wggm01/ISL-Maze-Solver-Robots/Robots/Fatima/GRAFICOS/SEGUNDO INTENTO.png

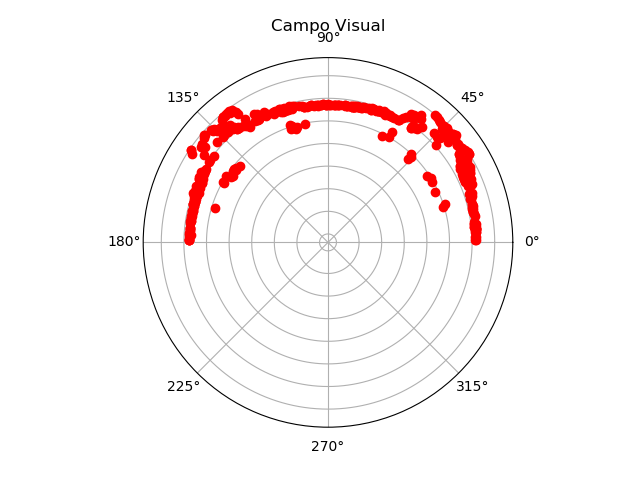
Robots/Fatima/GRAFICOS/SEGUNDO INTENTO.png
