wggm01/ISL-Maze-Solver-Robots/Robots/Fatima/IMUvi/data/texttest.png

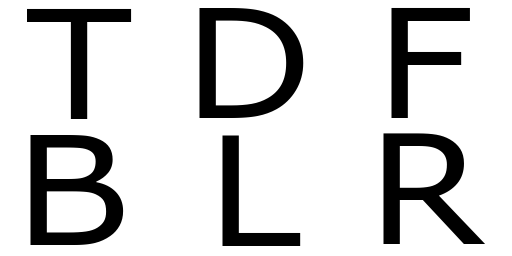
Robots/Fatima/IMUvi/data/texttest.png
