wggm01/ISL-Maze-Solver-Robots/Robots/Fatima/LSI.png

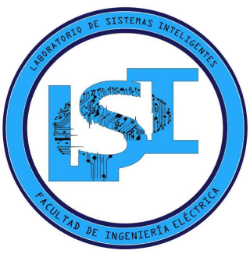
Robots/Fatima/LSI.png
