wggm01/ISL-Maze-Solver-Robots/Robots/Fatima/MEJORAS/3d83c7c686e7c798222806760055512f_1024x1024.png

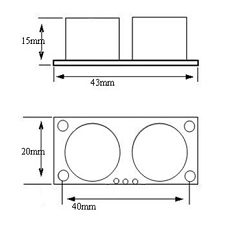
Robots/Fatima/MEJORAS/3d83c7c686e7c798222806760055512f_1024x1024.png
