wggm01/ISL-Maze-Solver-Robots/Robots/Fatima/MEJORAS/l298n.png

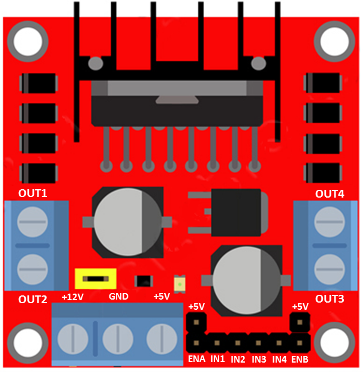
Robots/Fatima/MEJORAS/l298n.png
