wggm01/ISL-Maze-Solver-Robots/Robots/Fatima/MEJORAS/llanta definitiva.PNG

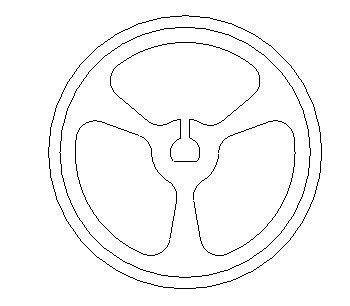
Robots/Fatima/MEJORAS/llanta definitiva.PNG
