wggm01/ISL-Maze-Solver-Robots/Robots/Fatima/MEJORAS/LLANTAS PARA SOPORTE EXTRAS.jpg

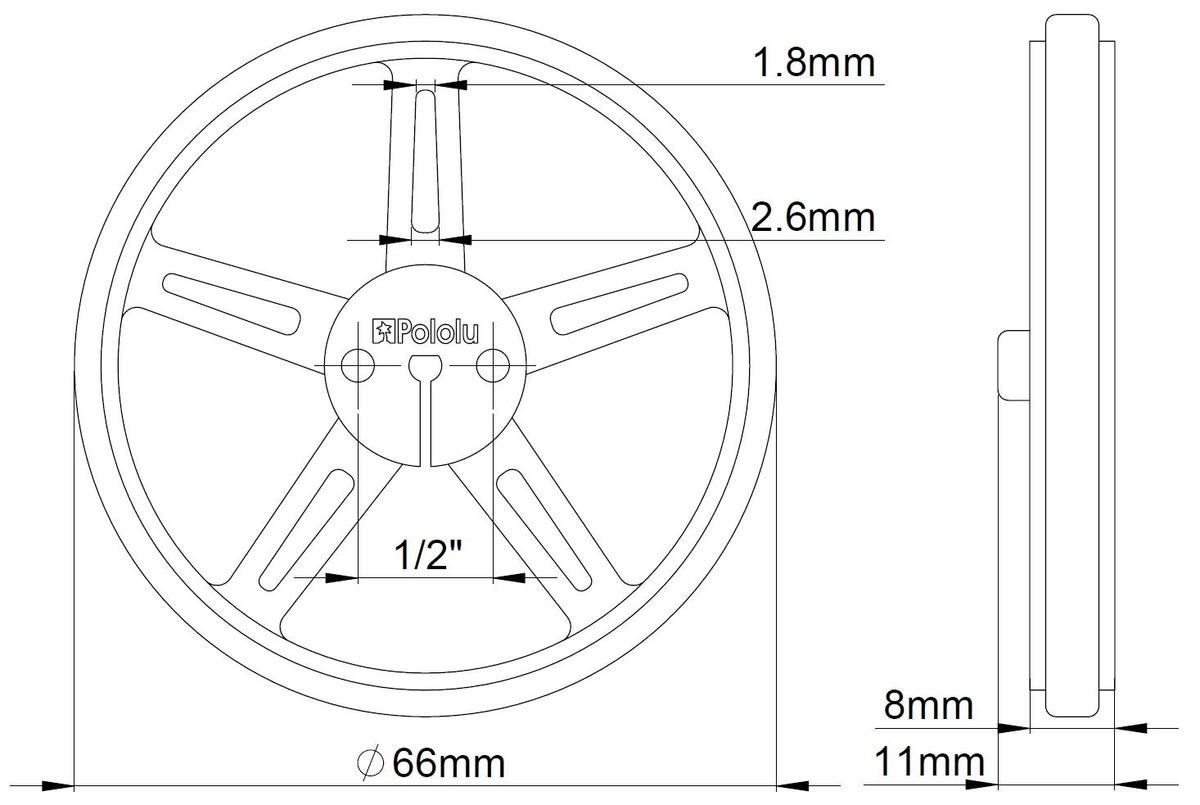
Robots/Fatima/MEJORAS/LLANTAS PARA SOPORTE EXTRAS.jpg
