wggm01/ISL-Maze-Solver-Robots/Robots/Fatima/MEJORAS/medidas servo.jpg

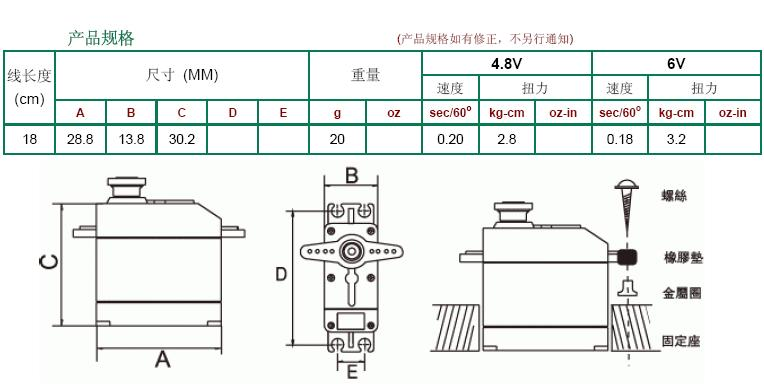
Robots/Fatima/MEJORAS/medidas servo.jpg
