wggm01/ISL-Maze-Solver-Robots/Robots/Fatima/MEJORAS/Nivel1.jpg

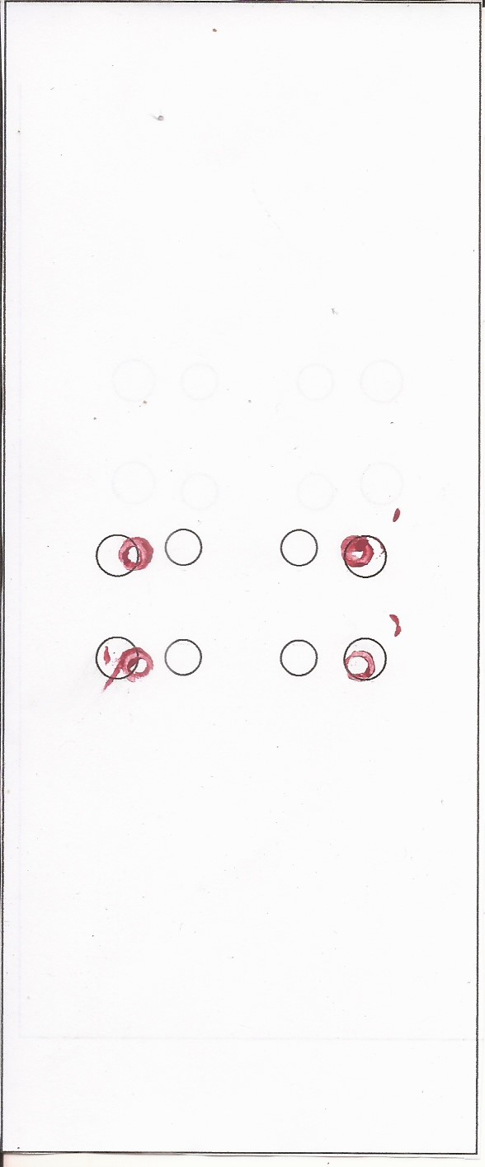
Robots/Fatima/MEJORAS/Nivel1.jpg
