wggm01/ISL-Maze-Solver-Robots/Robots/Fatima/MEJORAS/Nivel 3.jpg

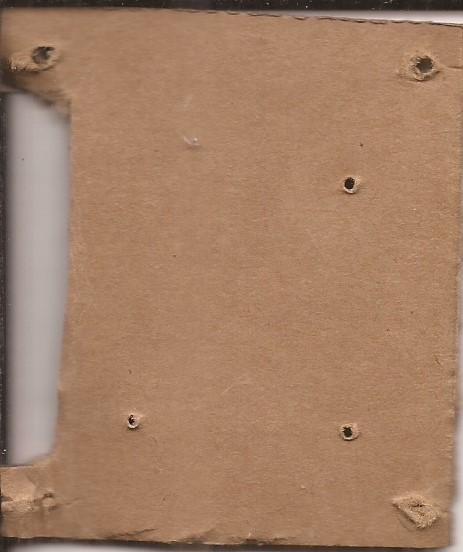
Robots/Fatima/MEJORAS/Nivel 3.jpg
