wggm01/ISL-Maze-Solver-Robots/Robots/Fatima/MEJORAS/NUEVA PCB MAY0 2019.png

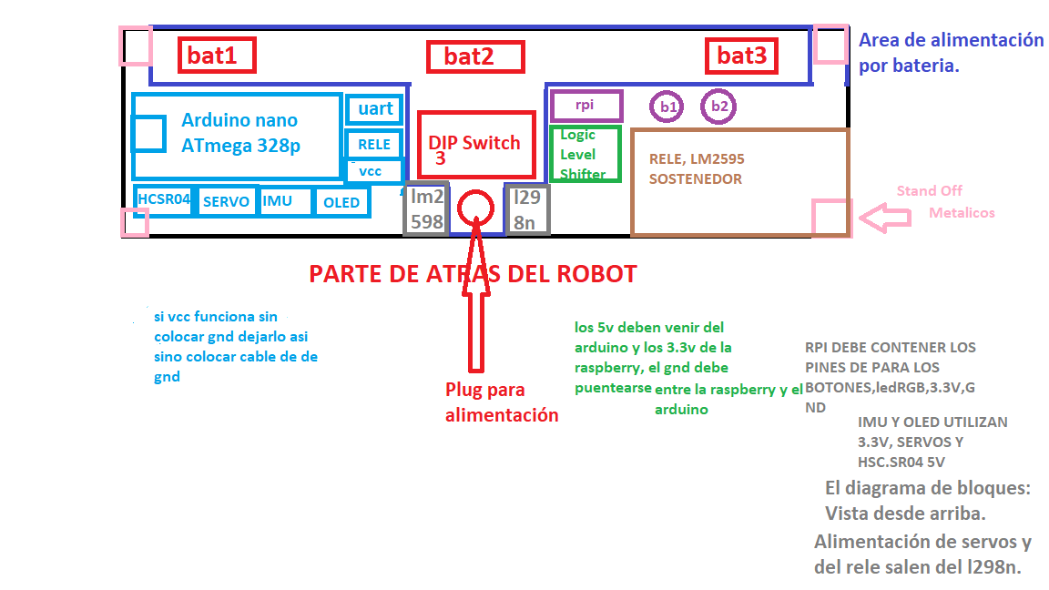
Robots/Fatima/MEJORAS/NUEVA PCB MAY0 2019.png
