wggm01/ISL-Maze-Solver-Robots/Robots/Fatima/MEJORAS/servo definitivo.PNG

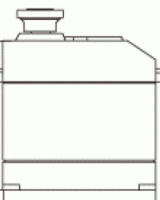
Robots/Fatima/MEJORAS/servo definitivo.PNG
