wggm01/ISL-Maze-Solver-Robots/Robots/Fatima/MEJORAS/union.jpg

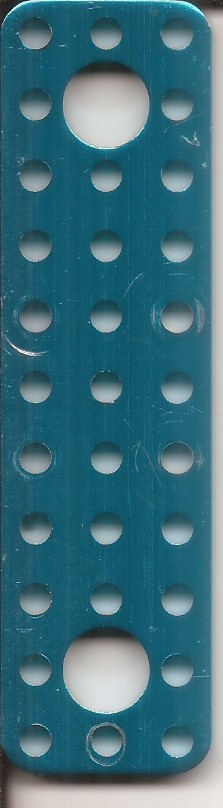
Robots/Fatima/MEJORAS/union.jpg
