wggm01/ISL-Maze-Solver-Robots/Robots/Gabriel/GCF-91B_1_/IMG_20181219_214946.jpg

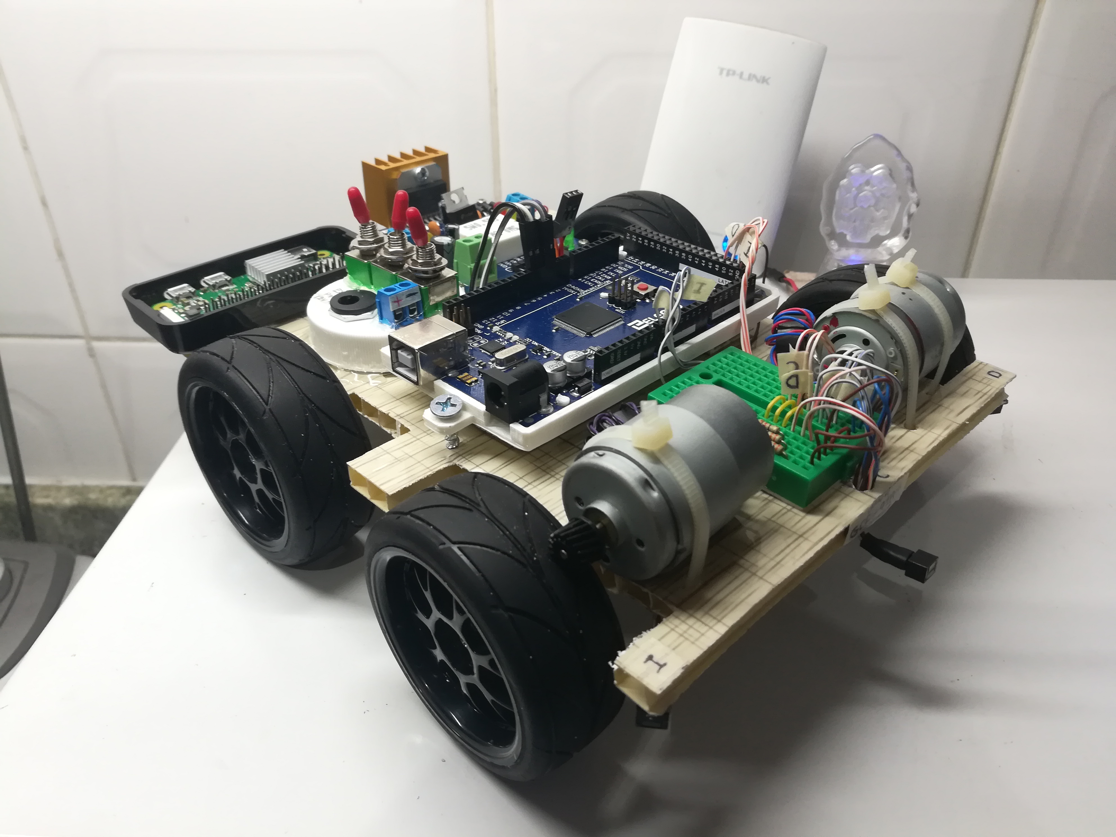
Robots/Gabriel/GCF-91B_1_/IMG_20181219_214946.jpg
