wggm01/ISL-Maze-Solver-Robots/Robots/Fatima/MEJORAS/sonar_cotas.dxf

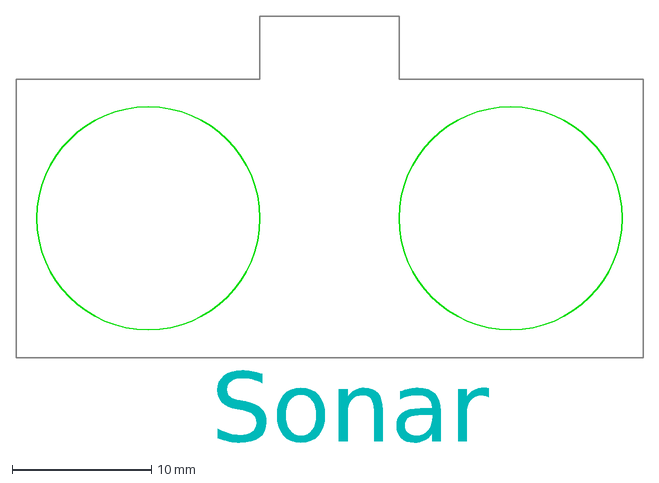
[picture p60: CAD file, 2019-03-16]
Robots/Fatima/MEJORAS/sonar_cotas.dxf
Sonar
