wggm01/ISL-Maze-Solver-Robots/Robots/Fatima/MEJORAS/CoverHCSR04.stl

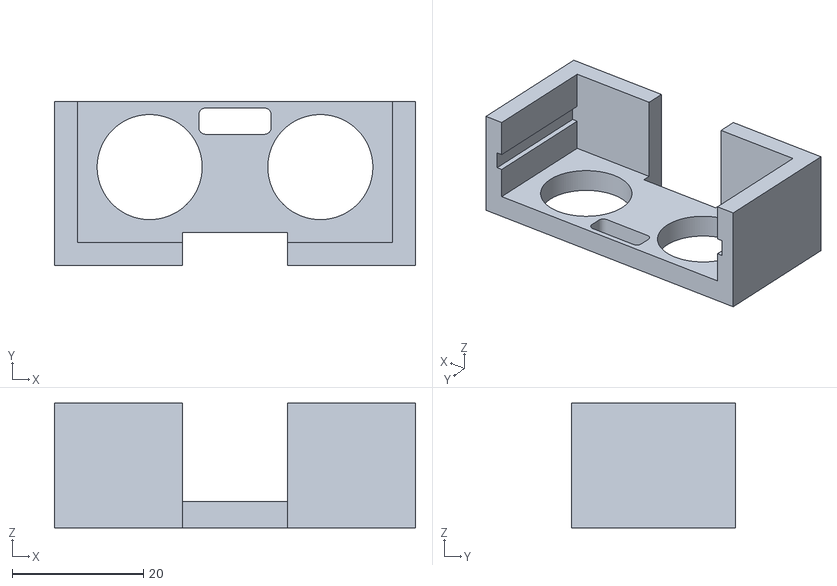
[picture p61: CAD file, 2019-03-16]
Robots/Fatima/MEJORAS/CoverHCSR04.stl
55.0 x 25.0 x 19.0
