wggm01/ISL-Maze-Solver-Robots/Robots/Fatima/MEJORAS/test ajuste HC-SR04.dxf

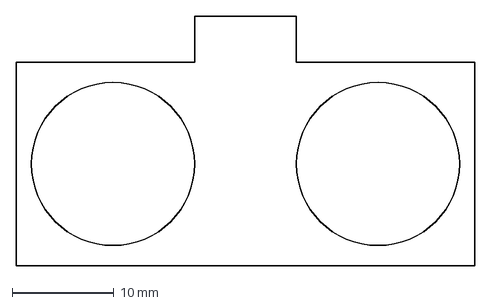
[picture p62: CAD file, 2019-03-16]
Robots/Fatima/MEJORAS/test ajuste HC-SR04.dxf
45.0 x 24.5 mm
