wggm01/ISL-Maze-Solver-Robots/Robots/Fatima/MEJORAS/Base Radar.stl

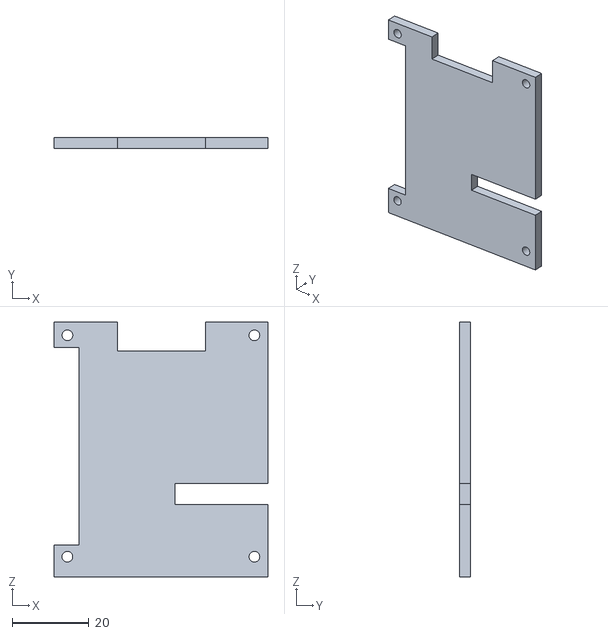
[picture p63: CAD file, 2019-03-16]
Robots/Fatima/MEJORAS/Base Radar.stl
55.8 x 3.00 x 66.6
