wggm01/ISL-Maze-Solver-Robots/Robots/Fatima/MEJORAS/Base para Servo.stl

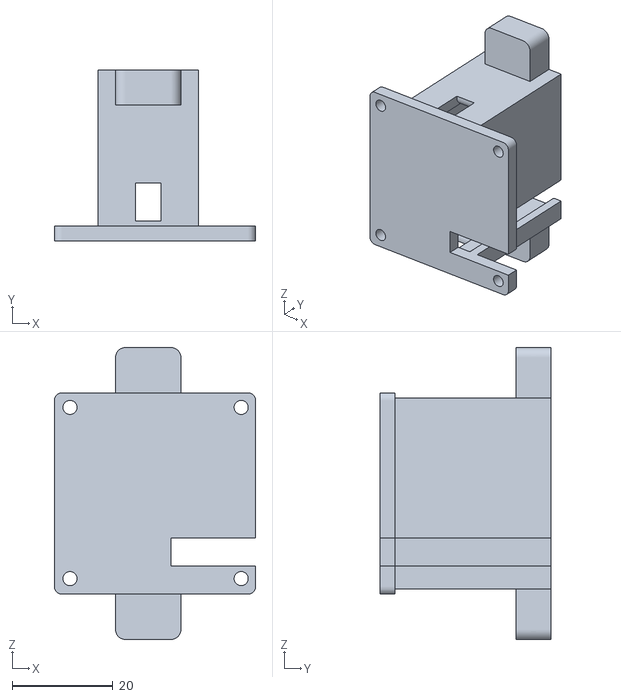
[picture p64: CAD file, 2019-03-16]
Robots/Fatima/MEJORAS/Base para Servo.stl
40.0 x 34.0 x 58.0
