wggm01/ISL-Maze-Solver-Robots/Robots/Fatima/MEJORAS/pcblocations.dxf

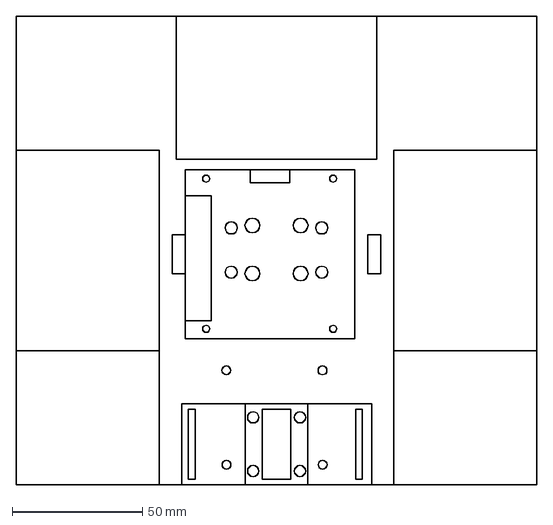
[picture p65: CAD file, 2019-03-12]
Robots/Fatima/MEJORAS/pcblocations.dxf
200.0 x 180.0 mm
