wggm01/ISL-Maze-Solver-Robots/Robots/Fatima/MEJORAS/pn2.dxf

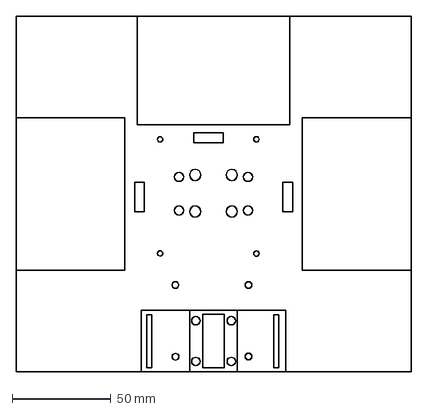
[picture p66: CAD file, 2019-03-12]
Robots/Fatima/MEJORAS/pn2.dxf
200.0 x 180.0 mm
