wggm01/ISL-Maze-Solver-Robots/Robots/Fatima/MEJORAS/pn1.dxf

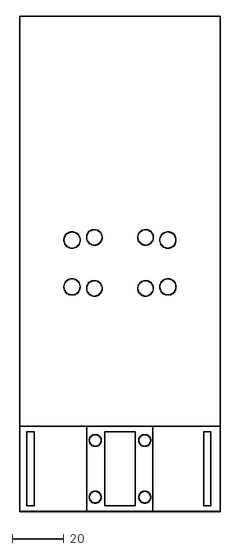
[picture p67: CAD file, 2019-03-12]
Robots/Fatima/MEJORAS/pn1.dxf
77.9 x 192.0
