wggm01/ISL-Maze-Solver-Robots/Robots/Fatima/MEJORAS/SISTEMA DE BATERIAS.dxf

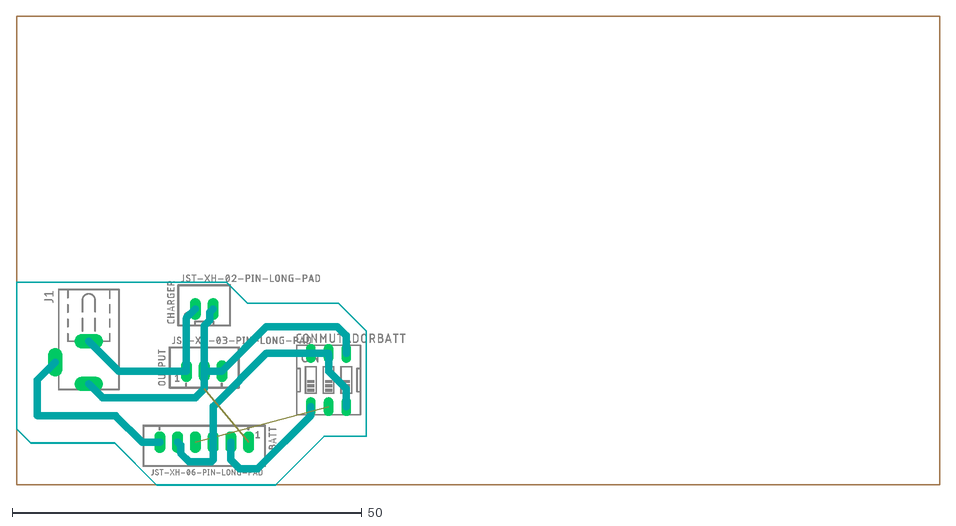
[picture p68: CAD file, 2019-03-03]
Robots/Fatima/MEJORAS/SISTEMA DE BATERIAS.dxf
132.1 x 67.1
