wggm01/ISL-Maze-Solver-Robots/Robots/Fatima/MEJORAS/CONTROL.dxf

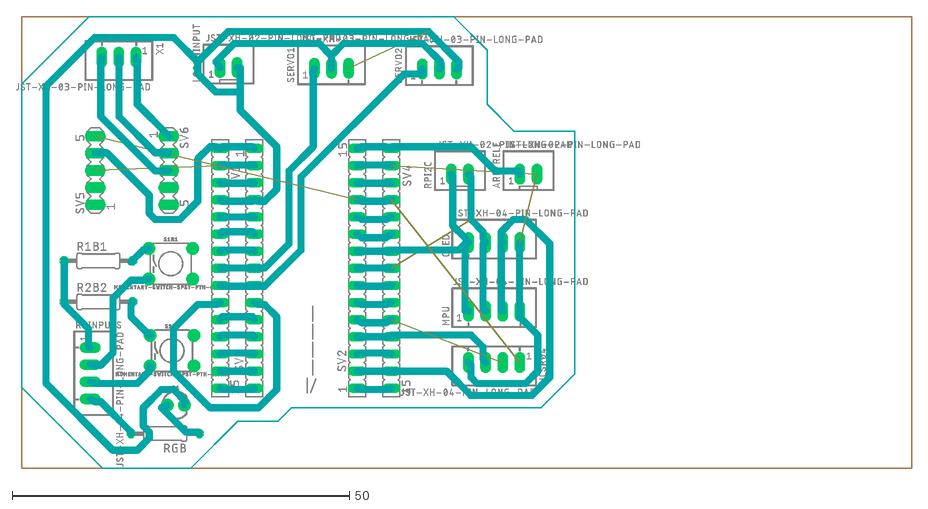
[picture p69: CAD file, 2019-03-03]
Robots/Fatima/MEJORAS/CONTROL.dxf
132.9 x 67.2
