wggm01/ISL-Maze-Solver-Robots/Robots/Fatima/GRAFICOS/test de paredes.png

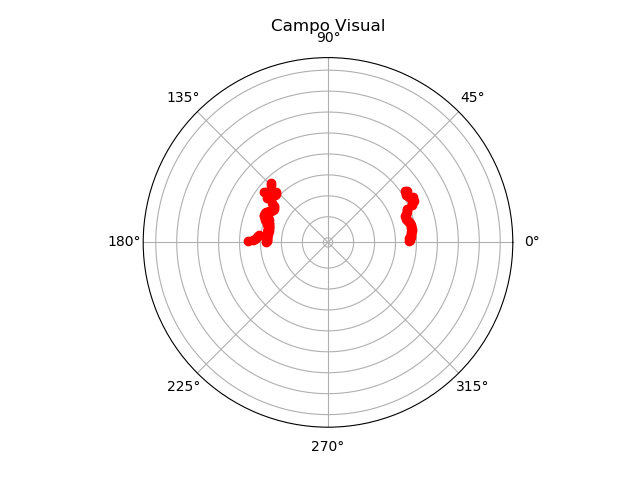
Robots/Fatima/GRAFICOS/test de paredes.png
