wggm01/ISL-Maze-Solver-Robots/Robots/Fatima/RESULTADOS ROBOT DE GUERRA/Giro a la derecha.jpeg

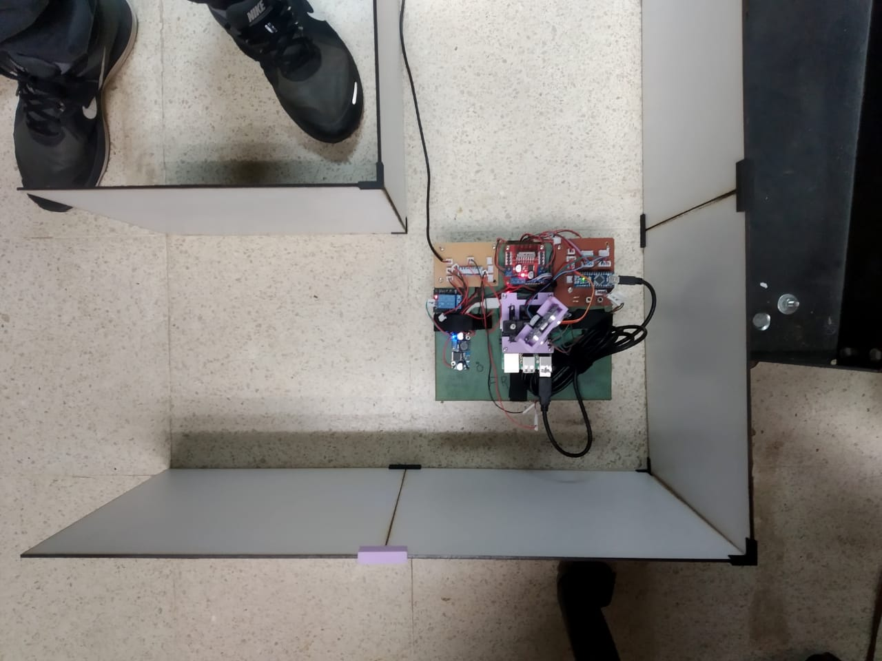
Robots/Fatima/RESULTADOS ROBOT DE GUERRA/Giro a la derecha.jpeg
