wggm01/ISL-Maze-Solver-Robots/Robots/Fatima/RESULTADOS ROBOT DE GUERRA/Seguir Recto.jpeg

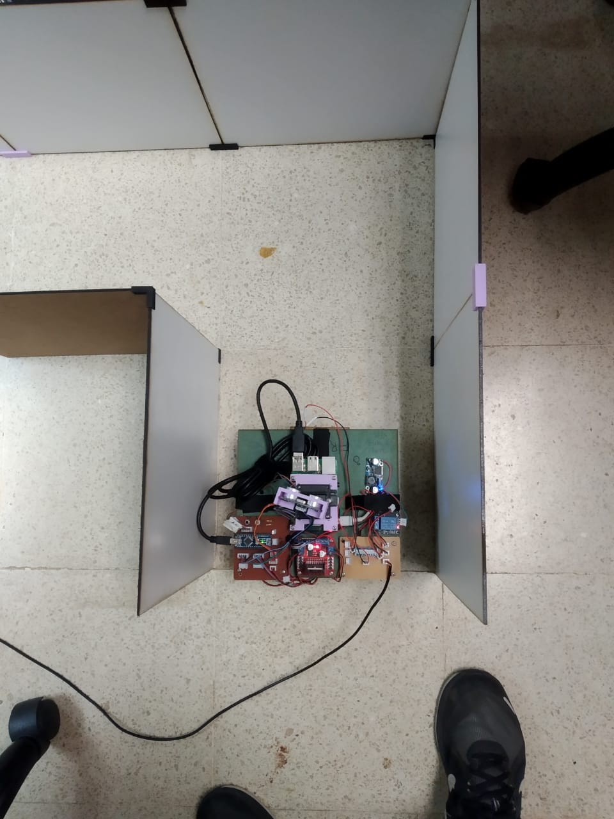
Robots/Fatima/RESULTADOS ROBOT DE GUERRA/Seguir Recto.jpeg
