wggm01/ISL-Maze-Solver-Robots/Robots/Fatima/GRAFICOS/issue.png

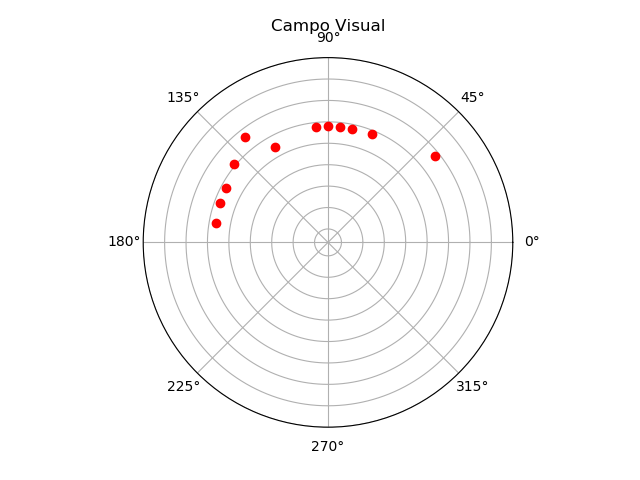
Robots/Fatima/GRAFICOS/issue.png
